J-IMPACT/PicoWaveDock/circuit/pico_wave_dock_v2.kicad_sch

## KiCad design circuit/pico_wave_dock_v2.kicad_sch (2026-04-12)

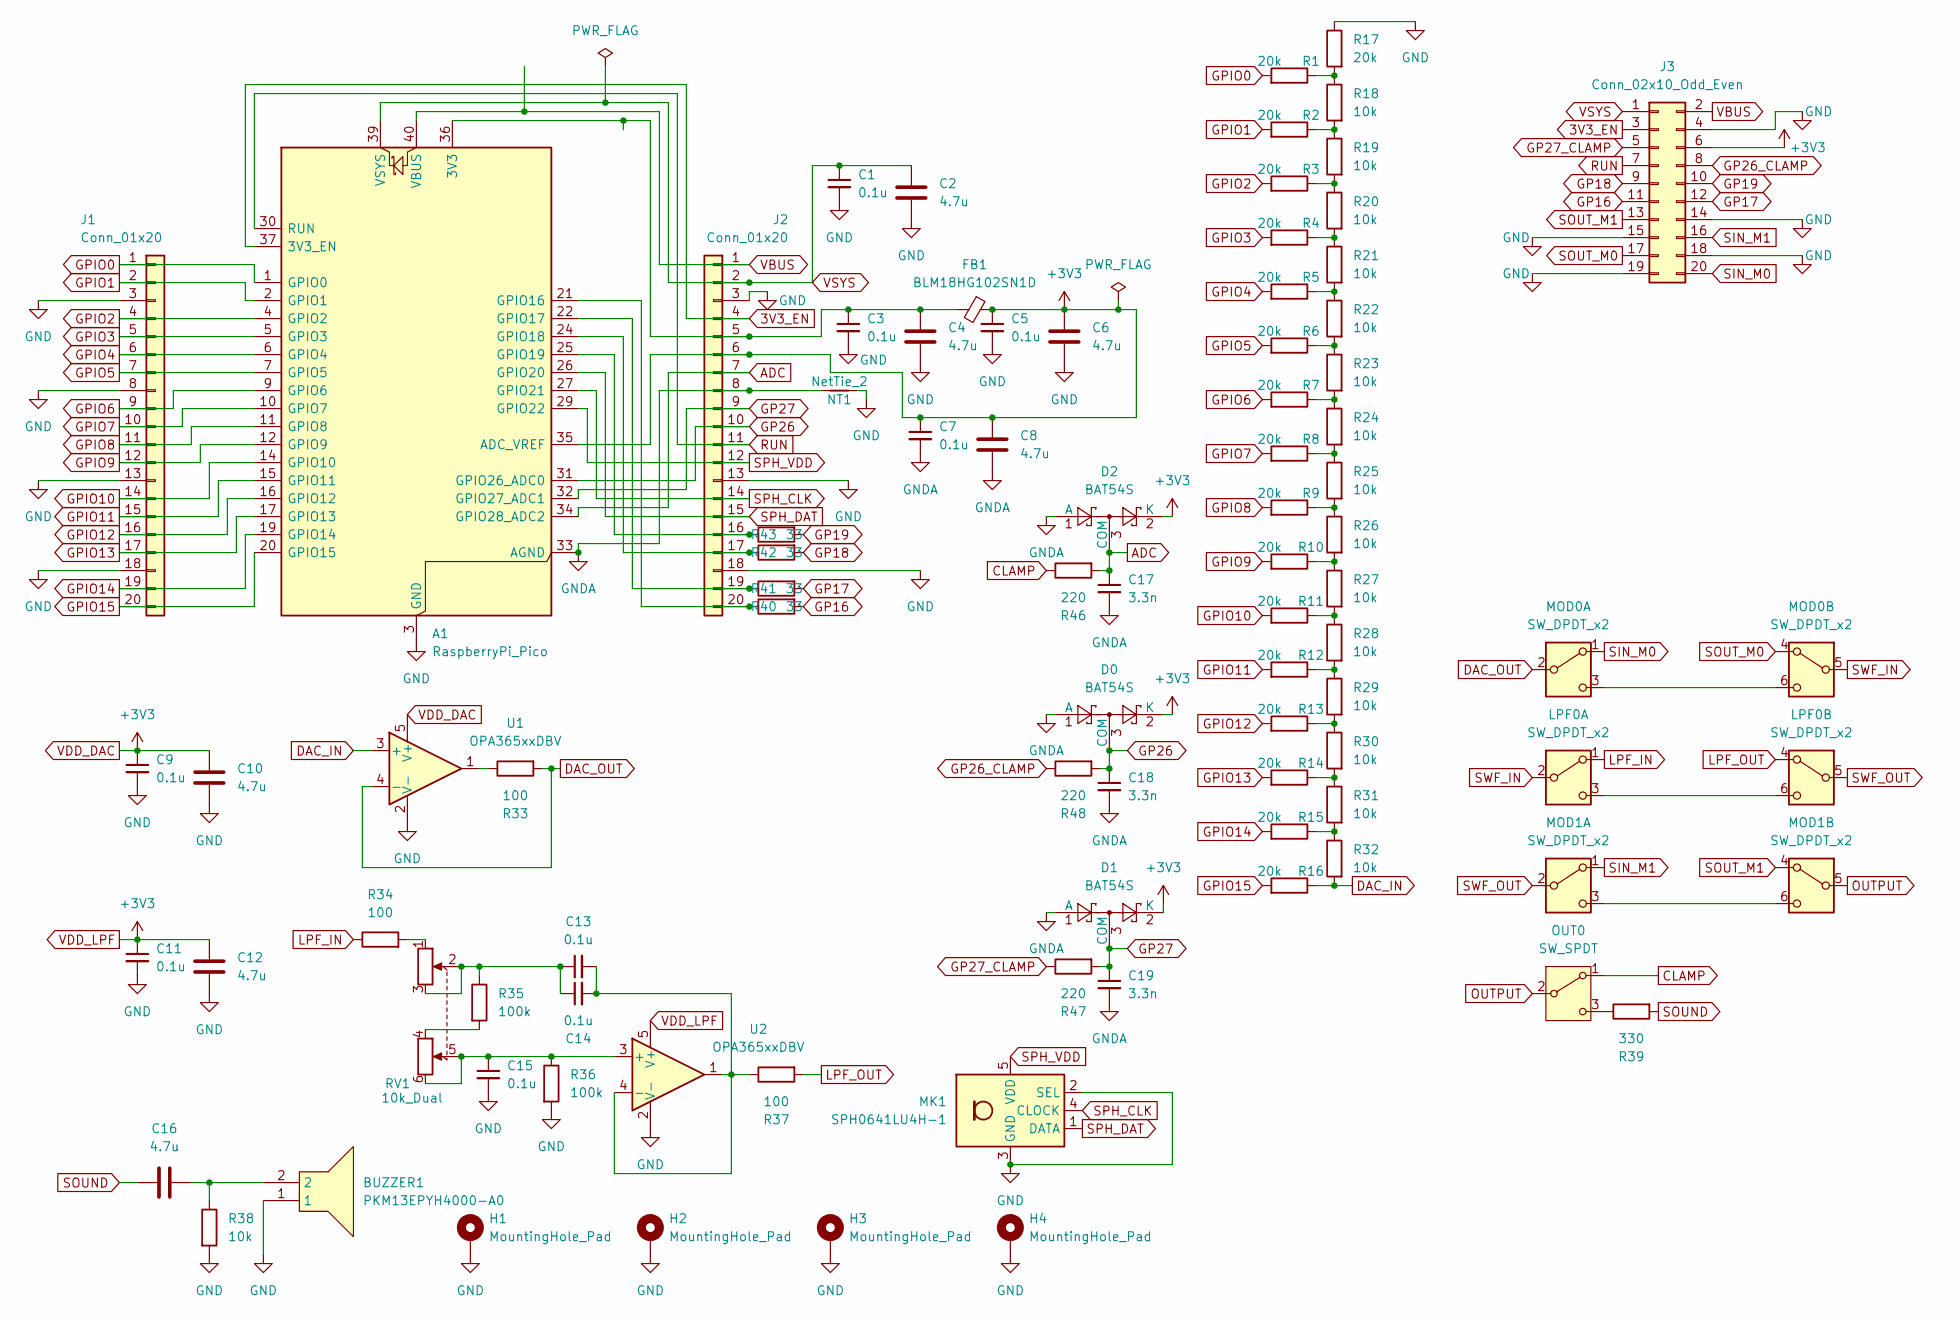
[picture p5: schematic pico_wave_dock_v2.kicad_sch]

Parts:
A1: RaspberryPi_Pico; RaspberryPi_Pico_Common_Unspecified
BUZZER1: PKM13EPYH4000-A0; BUZ-TH_BD12.6-P5.00-D0.5; LCSC Part C162678
C1, C3, C5, C7, C9, C11, C13, C14, C15: 0.1u; C_0603_1608Metric_Pad1.08x0.95mm_HandSolder
C2, C4, C6, C8, C10, C12, C16: 4.7u; C_0603_1608Metric_Pad1.08x0.95mm_HandSolder
C17, C18, C19: 3.3n; C_0603_1608Metric_Pad1.08x0.95mm_HandSolder
D0, D1, D2: BAT54S; SOT-23
FB1: BLM18HG102SN1D; L_0603_1608Metric_Pad1.05x0.95mm_HandSolder
H1, H2, H3, H4: MountingHole_Pad; MountingHole_2.2mm_M2_Pad_TopBottom
J1, J2: Conn_01x20; PinSocket_1x20_P2.54mm_Vertical
J3: Conn_02x10_Odd_Even; PinHeader_2x10_P2.54mm_Vertical
LPF0: SW_DPDT_x2; SW-SMD_MST22D18G2
MK1: SPH0641LU4H-1; MIC-SMD_5P_L3.5-W2.7-P0.82_SPH0641LU4H-1
MOD0, MOD1: SW_DPDT_x2; SW-SMD_MST22D18G2
NT1: NetTie_2; NetTie-2_SMD_Pad0.5mm
OUT0: SW_SPDT; SW-SMD_SHOUHAN_MST-22D18G23J_C2875122
R1, R2, R3, R4, R5, R6, R7, R8, R9, R10, R11, R12, R13, R14, R15, R16, R17: 20k; R_0603_1608Metric_Pad0.98x0.95mm_HandSolder
R18, R19, R20, R21, R22, R23, R24, R25, R26, R27, R28, R29, R30, R31, R32, R38: 10k; R_0603_1608Metric_Pad0.98x0.95mm_HandSolder
R33, R34, R37: 100; R_0603_1608Metric_Pad0.98x0.95mm_HandSolder
R35, R36: 100k; R_0603_1608Metric_Pad0.98x0.95mm_HandSolder
R39: 330; R_0603_1608Metric_Pad0.98x0.95mm_HandSolder
R40, R41, R42, R43: 33; R_0603_1608Metric_Pad0.98x0.95mm_HandSolder
R46, R47, R48: 220; R_0603_1608Metric_Pad0.98x0.95mm_HandSolder
RV1: 10k_Dual; RES-ADJ-TH_RK12L1230C1M
U1, U2: OPA365xxDBV; SOT-23-5

Connections:
3V3_EN: A1.37 (3V3_EN), J2.4, J3.3
+3V3: A1.35 (ADC_VREF), C5.1, C6.1, C7.1, C8.1, C9.1, C10.1, C11.1, C12.1, D0.2 (K), D1.2 (K), D2.2 (K), FB1.1, J2.6, J3.6, U1.5 (V+), U2.5 (V+)
ADC: A1.34 (GPIO28_ADC2), C17.1, D2.3 (COM), J2.7, R46.2
CLAMP: OUT0.1 (A), R46.1
DAC_IN: R16.1, R32.2, U1.3 (+)
DAC_OUT: MOD0.2 (B), R33.2, U1.4 (-)
GND: A1.3 (GND), A1.8 (GND), A1.13 (GND), A1.18 (GND), A1.23 (GND), A1.28 (GND), A1.38 (GND), BUZZER1.1, C1.2, C2.2, C3.2, C4.2, C5.2, C6.2, C9.2, C10.2, C11.2, C12.2, C15.2, H1.1, H2.1, H3.1, H4.1, J1.3, J1.8, J1.13, J1.18, J2.3, J2.13, J2.18, J3.4, J3.14, J3.15, J3.18, J3.19, MK1.2 (SEL), MK1.3 (GND), NT1.2, R17.1, R36.2, R38.2, U1.2 (V-), U2.2 (V-)
GNDA: A1.33 (AGND), C7.2, C8.2, C17.2, C18.2, C19.2, D0.1 (A), D1.1 (A), D2.1 (A), J2.8, NT1.1
GP16: J3.11, R40.2
GP17: J3.12, R41.2
GP18: J3.9, R42.2
GP19: J3.10, R43.2
GP26: A1.31 (GPIO26_ADC0), C18.1, D0.3 (COM), J2.10, R48.2
GP26_CLAMP: J3.8, R48.1
GP27: A1.32 (GPIO27_ADC1), C19.1, D1.3 (COM), J2.9, R47.2
GP27_CLAMP: J3.5, R47.1
GPIO0: A1.1 (GPIO0), J1.1, R1.2
GPIO1: A1.2 (GPIO1), J1.2, R2.2
GPIO2: A1.4 (GPIO2), J1.4, R3.2
GPIO3: A1.5 (GPIO3), J1.5, R4.2
GPIO4: A1.6 (GPIO4), J1.6, R5.2
GPIO5: A1.7 (GPIO5), J1.7, R6.2
GPIO6: A1.9 (GPIO6), J1.9, R7.2
GPIO7: A1.10 (GPIO7), J1.10, R8.2
GPIO8: A1.11 (GPIO8), J1.11, R9.2
GPIO9: A1.12 (GPIO9), J1.12, R10.2
GPIO10: A1.14 (GPIO10), J1.14, R11.2
GPIO11: A1.15 (GPIO11), J1.15, R12.2
GPIO12: A1.16 (GPIO12), J1.16, R13.2
GPIO13: A1.17 (GPIO13), J1.17, R14.2
GPIO14: A1.19 (GPIO14), J1.19, R15.2
GPIO15: A1.20 (GPIO15), J1.20, R16.2
LPF_IN: LPF0.1 (A), R34.1
LPF_OUT: LPF0.4 (A), R37.2
unnamed: A1.21 (GPIO16), J2.20, R40.1
unnamed: A1.22 (GPIO17), J2.19, R41.1
unnamed: A1.24 (GPIO18), J2.17, R42.1
unnamed: A1.25 (GPIO19), J2.16, R43.1
unnamed: A1.36 (3V3), C3.1, C4.1, FB1.2, J2.5
unnamed: BUZZER1.2, C16.2, R38.1
unnamed: C13.1, C14.1, R35.1, RV1.2, RV1.3
unnamed: C13.2, C14.2, R37.1, U2.1, U2.4 (-)
unnamed: C15.1, R36.1, RV1.5, RV1.6, U2.3 (+)
unnamed: LPF0.3 (C), LPF0.6 (C)
unnamed: MOD0.3 (C), MOD0.6 (C)
unnamed: MOD1.3 (C), MOD1.6 (C)
unnamed: OUT0.3 (C), R39.1
unnamed: R1.1, R17.2, R18.1
unnamed: R10.1, R26.2, R27.1
unnamed: R11.1, R27.2, R28.1
unnamed: R12.1, R28.2, R29.1
unnamed: R13.1, R29.2, R30.1
unnamed: R14.1, R30.2, R31.1
unnamed: R15.1, R31.2, R32.1
unnamed: R2.1, R18.2, R19.1
unnamed: R3.1, R19.2, R20.1
unnamed: R4.1, R20.2, R21.1
unnamed: R5.1, R21.2, R22.1
unnamed: R6.1, R22.2, R23.1
unnamed: R7.1, R23.2, R24.1
unnamed: R8.1, R24.2, R25.1
unnamed: R9.1, R25.2, R26.1
unnamed: R33.1, U1.1
unnamed: R34.2, RV1.1
unnamed: R35.2, RV1.4
OUTPUT: MOD1.5 (B), OUT0.2 (B)
RUN: A1.30 (RUN), J2.11, J3.7
SIN_M0: J3.20, MOD0.1 (A)
SIN_M1: J3.16, MOD1.1 (A)
SOUND: C16.1, R39.2
SOUT_M0: J3.17, MOD0.4 (A)
SOUT_M1: J3.13, MOD1.4 (A)
SPH_CLK: A1.27 (GPIO21), J2.14, MK1.4 (CLOCK)
SPH_DAT: A1.26 (GPIO20), J2.15, MK1.1 (DATA)
SPH_VDD: A1.29 (GPIO22), J2.12, MK1.5 (VDD)
SWF_IN: LPF0.2 (B), MOD0.5 (B)
SWF_OUT: LPF0.5 (B), MOD1.2 (B)
VBUS: A1.40 (VBUS), J2.1, J3.2
VSYS: A1.39 (VSYS), C1.1, C2.1, J2.2, J3.1
