J-IMPACT/PicoWaveDock/open-source-silicon-magazine-vol2/circuit/pico_wave_dock_ishikai.kicad_sch

## KiCad design open-source-silicon-magazine-vol2/circuit/pico_wave_dock_ishikai.kicad_sch (2026-04-12)

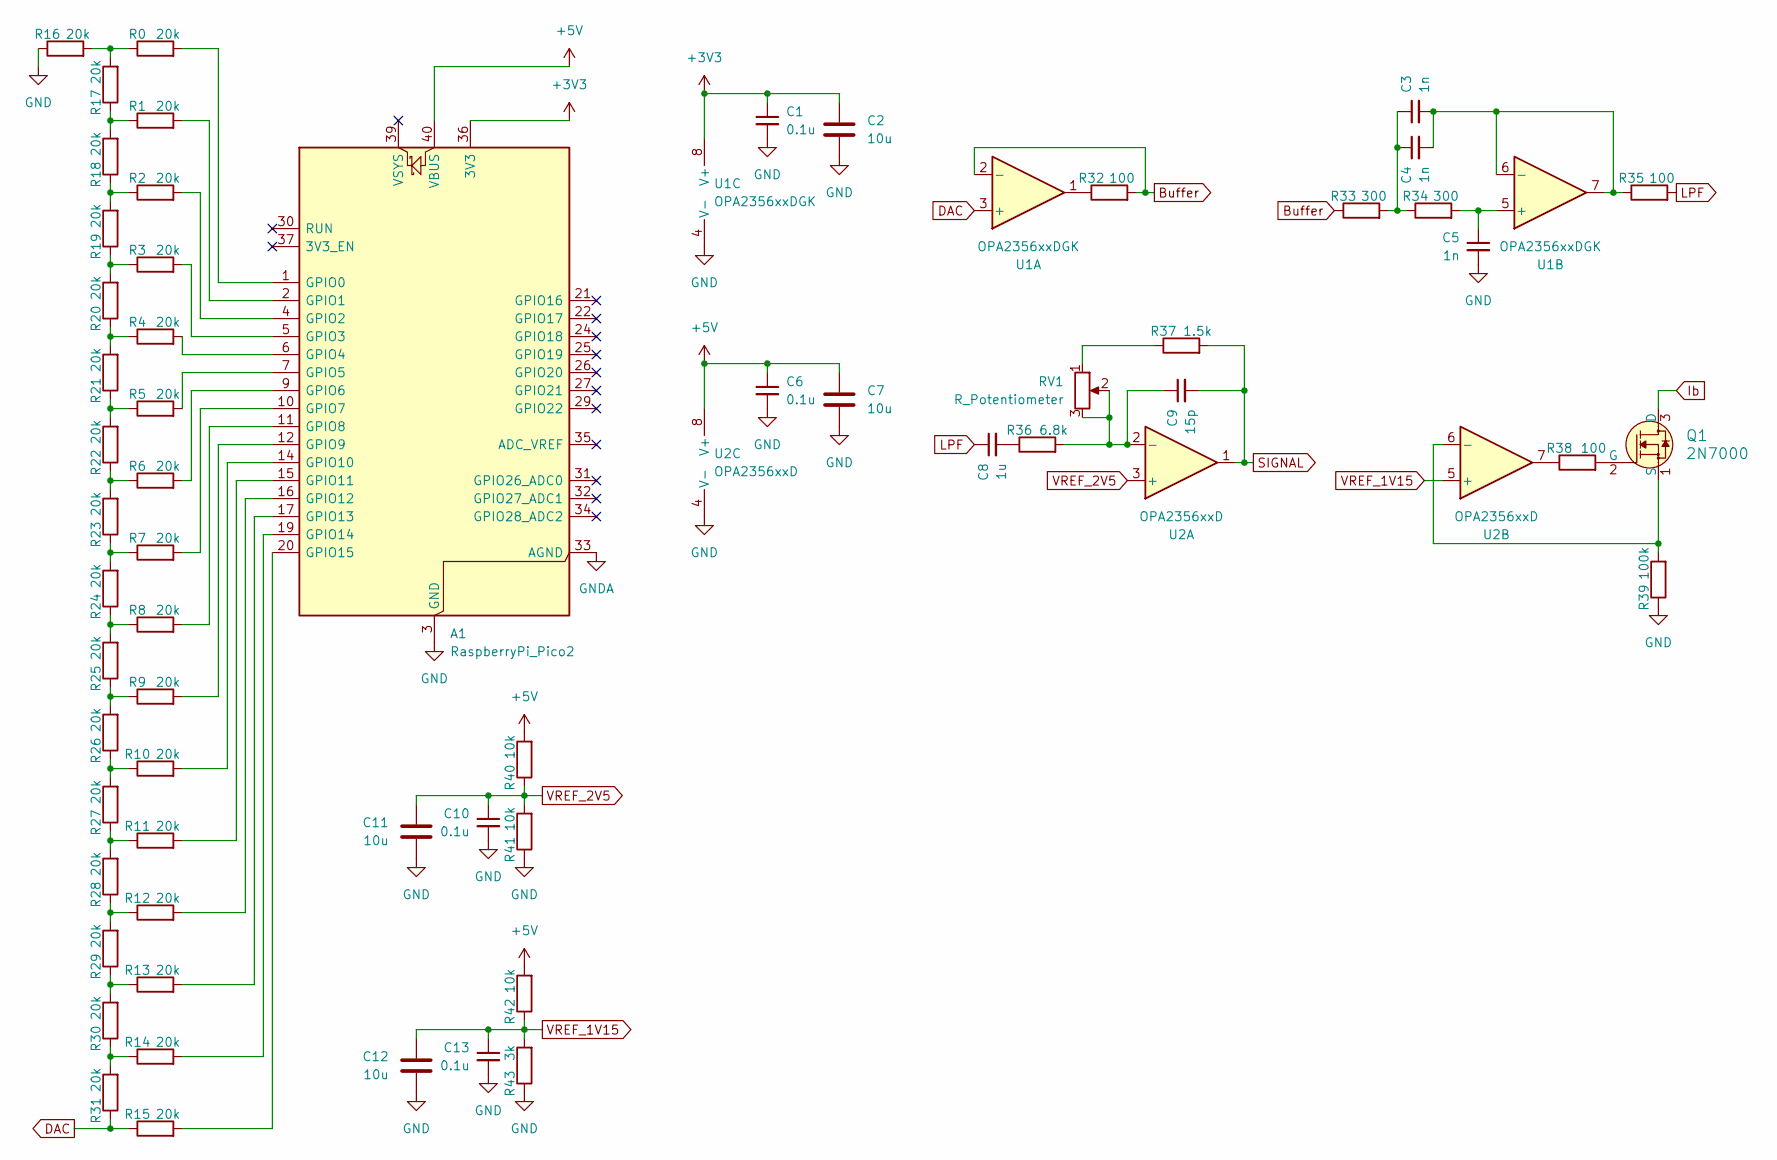
[picture p6: schematic pico_wave_dock_ishikai.kicad_sch]

Parts:
A1: RaspberryPi_Pico2; RaspberryPi_Pico_Common_Unspecified
C1, C6, C10, C13: 0.1u; C_0603_1608Metric_Pad1.08x0.95mm_HandSolder
C2, C7, C11, C12: 10u; C_0603_1608Metric_Pad1.08x0.95mm_HandSolder
C3, C4, C5: 1n; C_0603_1608Metric_Pad1.08x0.95mm_HandSolder
C8: 1u; C_0603_1608Metric_Pad1.08x0.95mm_HandSolder
C9: 15p; C_0603_1608Metric_Pad1.08x0.95mm_HandSolder
Q1: 2N7000; TO-92-3; MPN 2N7000; Digi-Key_PN 2N7000FS-ND
R0, R1, R2, R3, R4, R5, R6, R7, R8, R9, R10, R11, R12, R13, R14, R15, R16, R17, R18, R19, R20, R21, R22, R23, R24, R25, R26, R27, R28, R29, R30, R31: 20k; R_0603_1608Metric_Pad0.98x0.95mm_HandSolder
R32, R35, R38: 100; R_0603_1608Metric_Pad0.98x0.95mm_HandSolder
R33, R34: 300; R_0603_1608Metric_Pad0.98x0.95mm_HandSolder
R36: 6.8k; R_0603_1608Metric_Pad0.98x0.95mm_HandSolder
R37: 1.5k; R_0603_1608Metric_Pad0.98x0.95mm_HandSolder
R39: 100k; R_0603_1608Metric_Pad0.98x0.95mm_HandSolder
R40, R41, R42: 10k; R_0603_1608Metric_Pad0.98x0.95mm_HandSolder
R43: 3k; R_0603_1608Metric_Pad0.98x0.95mm_HandSolder
RV1: R_Potentiometer; Potentiometer_Alpha_RD901F-40-00D_Single_Vertical
U1: OPA2356xxDGK; SOIC-8_3.9x4.9mm_P1.27mm
U2: OPA2356xxD; SOIC-8_3.9x4.9mm_P1.27mm

Connections:
+3V3: A1.36 (3V3), C1.1, C2.1, U1.8 (V+)
+5V: A1.40 (VBUS), C6.1, C7.1, R40.2, R42.2, U2.8 (V+)
Buffer: R32.2, R33.1, U1.2 (-)
DAC: R15.1, R31.1, U1.3 (+)
GND: A1.3 (GND), A1.8 (GND), A1.13 (GND), A1.18 (GND), A1.23 (GND), A1.28 (GND), A1.38 (GND), C1.2, C2.2, C5.2, C6.2, C7.2, C10.2, C11.2, C12.2, C13.2, R16.1, R39.1, R41.1, R43.1, U1.4 (V-), U2.4 (V-)
GNDA: A1.33 (AGND)
Ib: Q1.3 (D)
LPF: C8.1, R35.2
unnamed: A1.1 (GPIO0), R0.2
unnamed: A1.2 (GPIO1), R1.2
unnamed: A1.4 (GPIO2), R2.2
unnamed: A1.5 (GPIO3), R3.2
unnamed: A1.6 (GPIO4), R4.2
unnamed: A1.7 (GPIO5), R5.2
unnamed: A1.9 (GPIO6), R6.2
unnamed: A1.10 (GPIO7), R7.2
unnamed: A1.11 (GPIO8), R8.2
unnamed: A1.12 (GPIO9), R9.2
unnamed: A1.14 (GPIO10), R10.2
unnamed: A1.15 (GPIO11), R11.2
unnamed: A1.16 (GPIO12), R12.2
unnamed: A1.17 (GPIO13), R13.2
unnamed: A1.19 (GPIO14), R14.2
unnamed: A1.20 (GPIO15), R15.2
unnamed: C3.1, C4.1, R33.2, R34.1
unnamed: C3.2, C4.2, R35.1, U1.6 (-), U1.7
unnamed: C5.1, R34.2, U1.5 (+)
unnamed: C8.2, R36.1
unnamed: C9.1, R36.2, RV1.2, RV1.3, U2.2 (-)
unnamed: Q1.1 (S), R39.2, U2.6 (-)
unnamed: Q1.2 (G), R38.2
unnamed: R0.1, R16.2, R17.2
unnamed: R1.1, R17.1, R18.2
unnamed: R10.1, R26.1, R27.2
unnamed: R11.1, R27.1, R28.2
unnamed: R12.1, R28.1, R29.2
unnamed: R13.1, R29.1, R30.2
unnamed: R14.1, R30.1, R31.2
unnamed: R2.1, R18.1, R19.2
unnamed: R3.1, R19.1, R20.2
unnamed: R4.1, R20.1, R21.2
unnamed: R5.1, R21.1, R22.2
unnamed: R6.1, R22.1, R23.2
unnamed: R7.1, R23.1, R24.2
unnamed: R8.1, R24.1, R25.2
unnamed: R9.1, R25.1, R26.2
unnamed: R32.1, U1.1
unnamed: R37.1, RV1.1
unnamed: R38.1, U2.7
SIGNAL: C9.2, R37.2, U2.1
VREF_1V15: C12.1, C13.1, R42.1, R43.2, U2.5 (+)
VREF_2V5: C10.1, C11.1, R40.1, R41.2, U2.3 (+)
