J-IMPACT/PicoWaveDock/wave_example/src/tables.rs

const LUT_BITS: u32 = 12;
const LUT_LEN: usize = 1 << LUT_BITS;

#[unsafe(link_section = ".data")]
pub static SINE_LUT: [u16; LUT_LEN] = [
	32768, 32818, 32868, 32918, 32969, 33019, 33069, 33119,
	33170, 33220, 33270, 33320, 33371, 33421, 33471, 33521,
	33572, 33622, 33672, 33722, 33773, 33823, 33873, 33923,
	33974, 34024, 34074, 34124, 34175, 34225, 34275, 34325,
	34375, 34426, 34476, 34526, 34576, 34626, 34677, 34727,
	34777, 34827, 34877, 34927, 34978, 35028, 35078, 35128,
	35178, 35228, 35278, 35328, 35379, 35429, 35479, 35529,
	35579, 35629, 35679, 35729, 35779, 35829, 35879, 35929,
	35979, 36029, 36079, 36129, 36179, 36229, 36279, 36329,
	36379, 36429, 36479, 36529, 36579, 36629, 36679, 36729,
	36779, 36829, 36878, 36928, 36978, 37028, 37078, 37128,
	37177, 37227, 37277, 37327, 37377, 37426, 37476, 37526,
	37576, 37625, 37675, 37725, 37774, 37824, 37874, 37923,
	37973, 38023, 38072, 38122, 38171, 38221, 38271, 38320,
	38370, 38419, 38469, 38518, 38568, 38617, 38666, 38716,
	38765, 38815, 38864, 38914, 38963, 39012, 39062, 39111,
	39160, 39210, 39259, 39308, 39357, 39407, 39456, 39505,
	39554, 39603, 39652, 39702, 39751, 39800, 39849, 39898,
	39947, 39996, 40045, 40094, 40143, 40192, 40241, 40290,
	40339, 40388, 40437, 40485, 40534, 40583, 40632, 40681,
	40729, 40778, 40827, 40876, 40924, 40973, 41022, 41070,
	41119, 41168, 41216, 41265, 41313, 41362, 41410, 41459,
	41507, 41556, 41604, 41652, 41701, 41749, 41797, 41846,
	41894, 41942, 41991, 42039, 42087, 42135, 42183, 42231,
	42280, 42328, 42376, 42424, 42472, 42520, 42568, 42616,
	42664, 42712, 42759, 42807, 42855, 42903, 42951, 42998,
	43046, 43094, 43142, 43189, 43237, 43285, 43332, 43380,
	43427, 43475, 43522, 43570, 43617, 43665, 43712, 43759,
	43807, 43854, 43901, 43949, 43996, 44043, 44090, 44137,
	44184, 44232, 44279, 44326, 44373, 44420, 44467, 44514,
	44561, 44607, 44654, 44701, 44748, 44795, 44841, 44888,
	44935, 44981, 45028, 45075, 45121, 45168, 45214, 45261,
	45307, 45354, 45400, 45446, 45493, 45539, 45585, 45632,
	45678, 45724, 45770, 45816, 45862, 45908, 45954, 46000,
	46046, 46092, 46138, 46184, 46230, 46276, 46322, 46367,
	46413, 46459, 46504, 46550, 46596, 46641, 46687, 46732,
	46778, 46823, 46868, 46914, 46959, 47004, 47050, 47095,
	47140, 47185, 47230, 47275, 47320, 47366, 47410, 47455,
	47500, 47545, 47590, 47635, 47680, 47724, 47769, 47814,
	47858, 47903, 47948, 47992, 48037, 48081, 48125, 48170,
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
];
